74ls00/GameKB/Datasheet/HTK1087B/htk1087b_kb.png

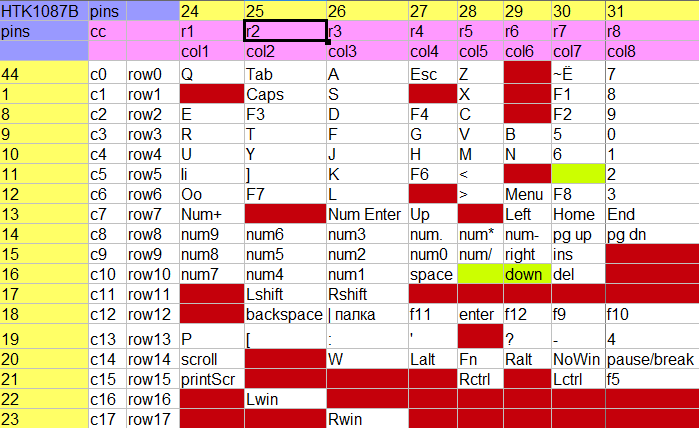
Datasheet/HTK1087B/htk1087b_kb.png
