74ls00/GameKB/Datasheet/HTK1087B/temp1.png

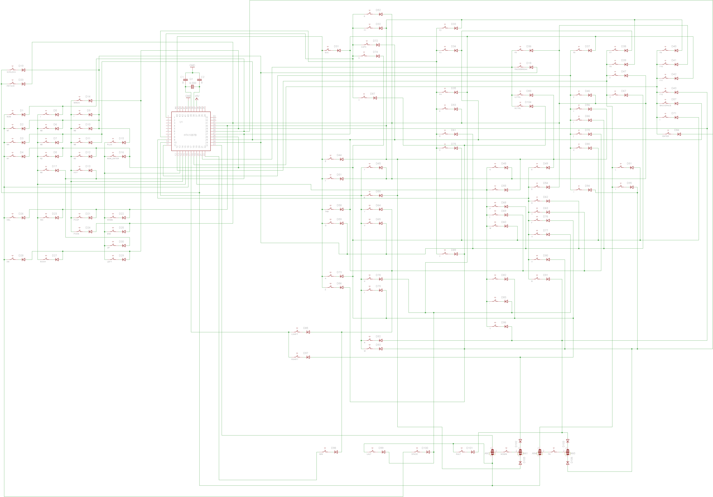
Datasheet/HTK1087B/temp1.png
