74ls00/GameKB/Datasheet/HTK1087B/temp2.png

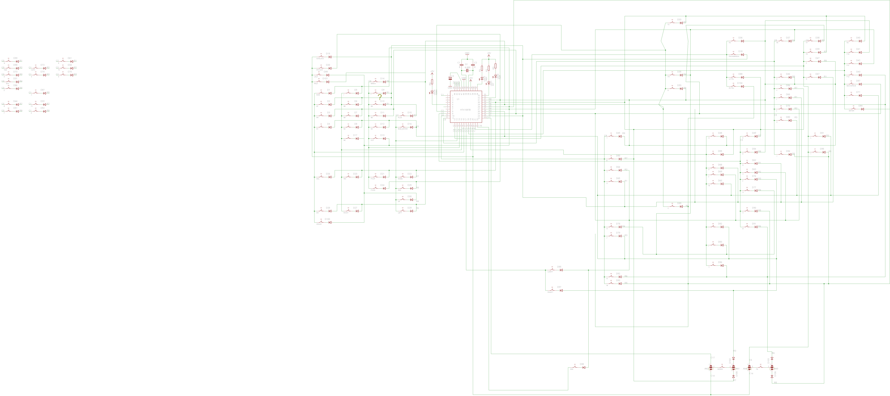
Datasheet/HTK1087B/temp2.png
