74ls00/GameKB/Model/Controller.bmp

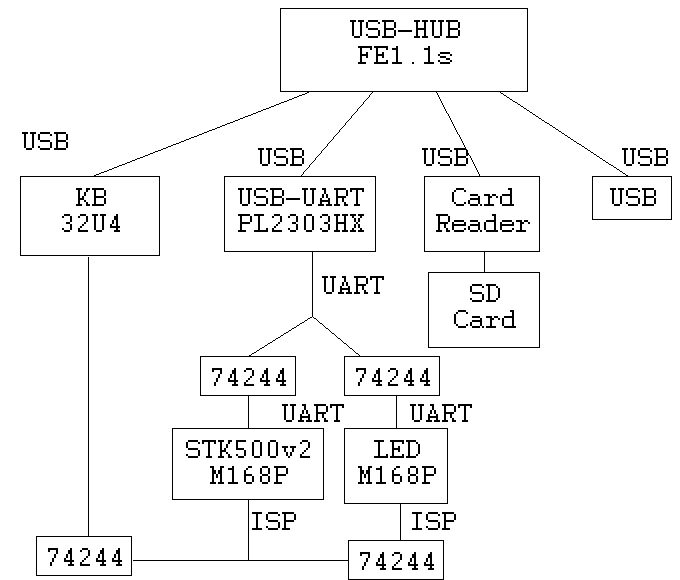
Model/Controller.bmp
