74ls00/GameKB/Model/html/2/Безымянный.png

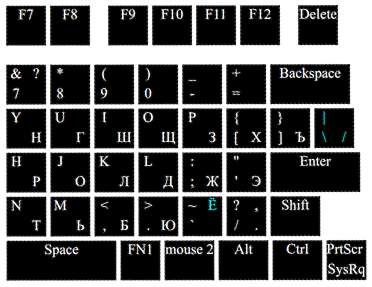
Model/html/2/Безымянный.png
