74ls00/GameKB/Model/html/pic/2.png

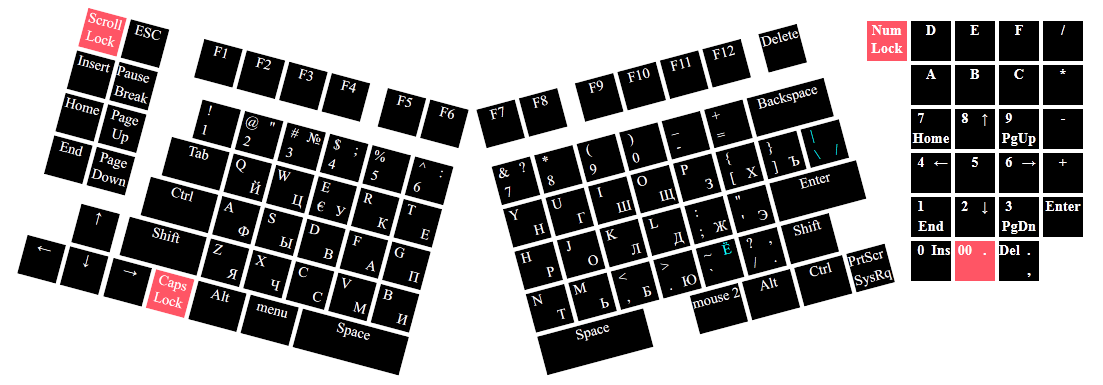
Model/html/pic/2.png
