74ls00/GameKB/Model/key-size/key-size.png

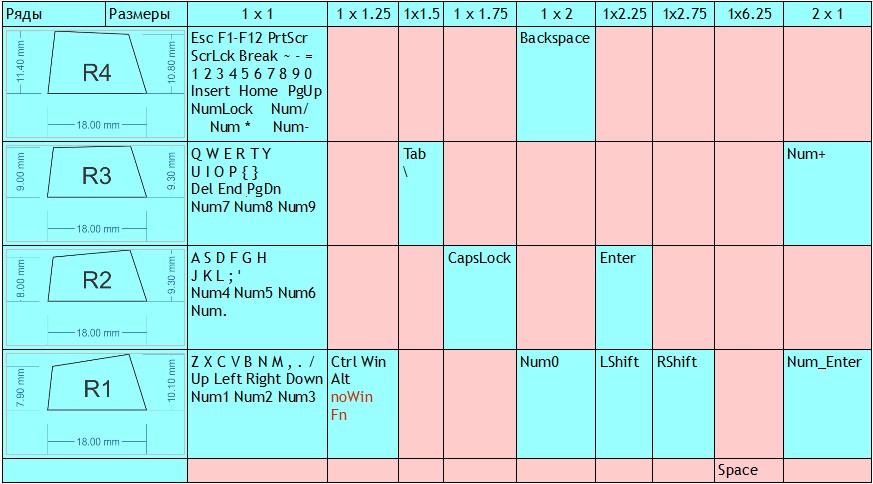
Model/key-size/key-size.png
