74ls00/GameKB/PCB/Controller/png/1.png

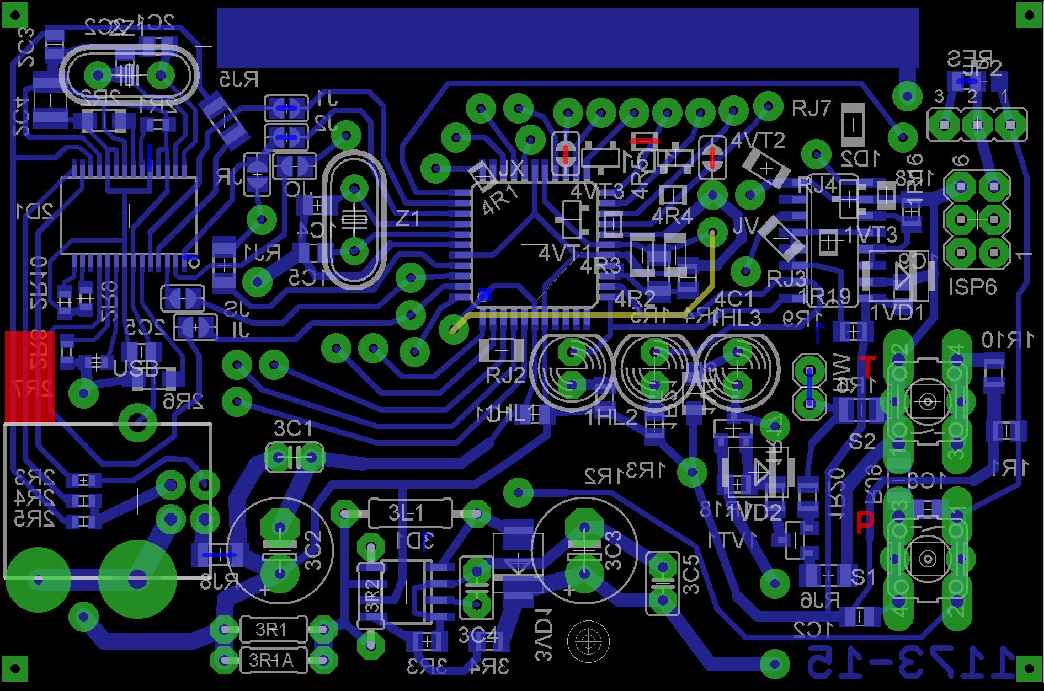
PCB/Controller/png/1.png
