74ls00/GameKB/PCB/Controller/png/1_cr.png

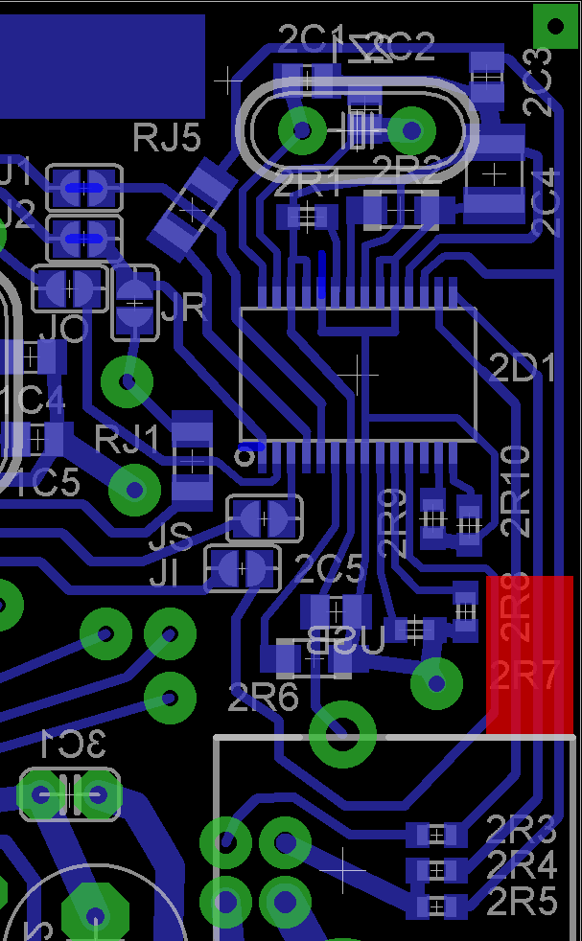
PCB/Controller/png/1_cr.png
