74ls00/GameKB/PCB/Controller/png/101.png

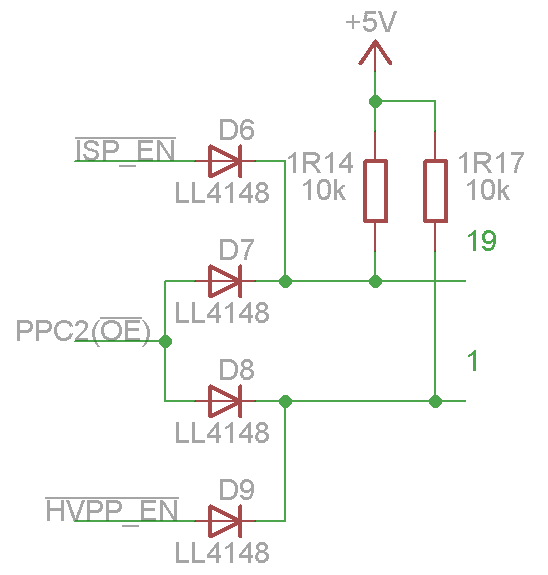
PCB/Controller/png/101.png
