74ls00/GameKB/PCB/Controller/png/102.png

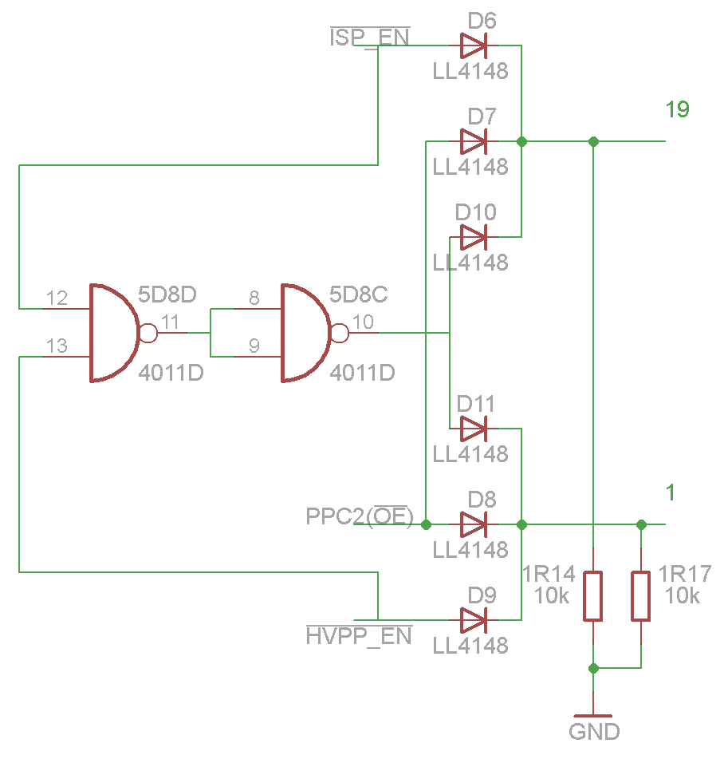
PCB/Controller/png/102.png
