74ls00/GameKB/PCB/Details/enter/HTB1JWZuLXXXXXa.aXXXq6xXFXXX5.jpg

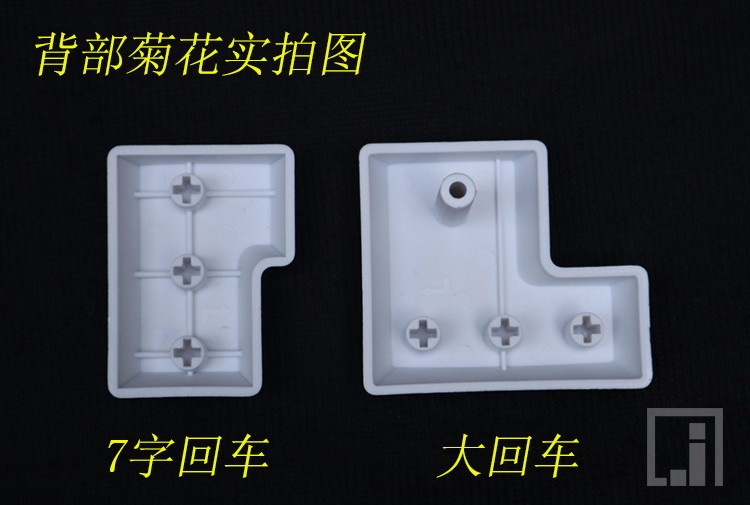
PCB/Details/enter/HTB1JWZuLXXXXXa.aXXXq6xXFXXX5.jpg
