74ls00/GameKB/PCB/Details/enter/HTB1tJs0LXXXXXXZXXXXq6xXFXXXk.jpg

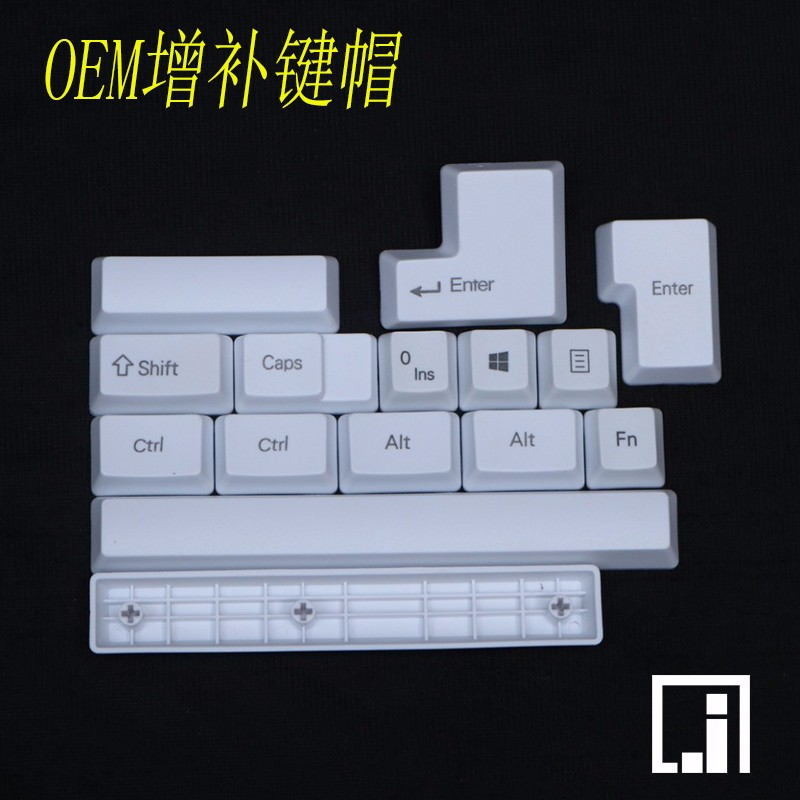
PCB/Details/enter/HTB1tJs0LXXXXXXZXXXXq6xXFXXXk.jpg
