74ls00/GameKB/PCB/Details/stabilizer_frame/stabilizer_frame_i.png

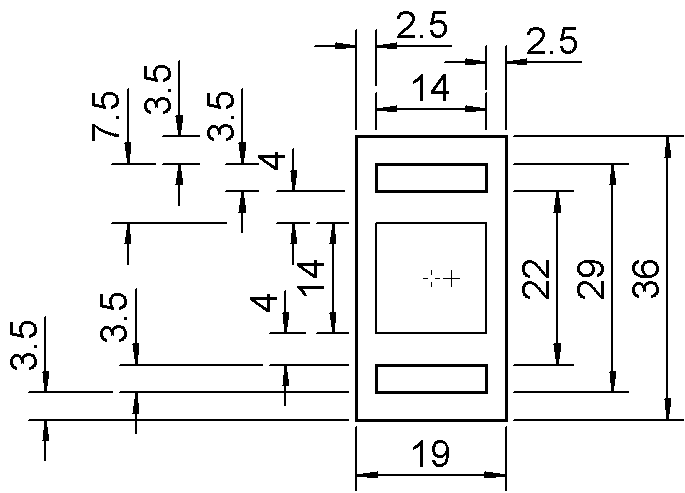
PCB/Details/stabilizer_frame/stabilizer_frame_i.png
