74ls00/GameKB/PCB/keyBoard_A/png/104.png

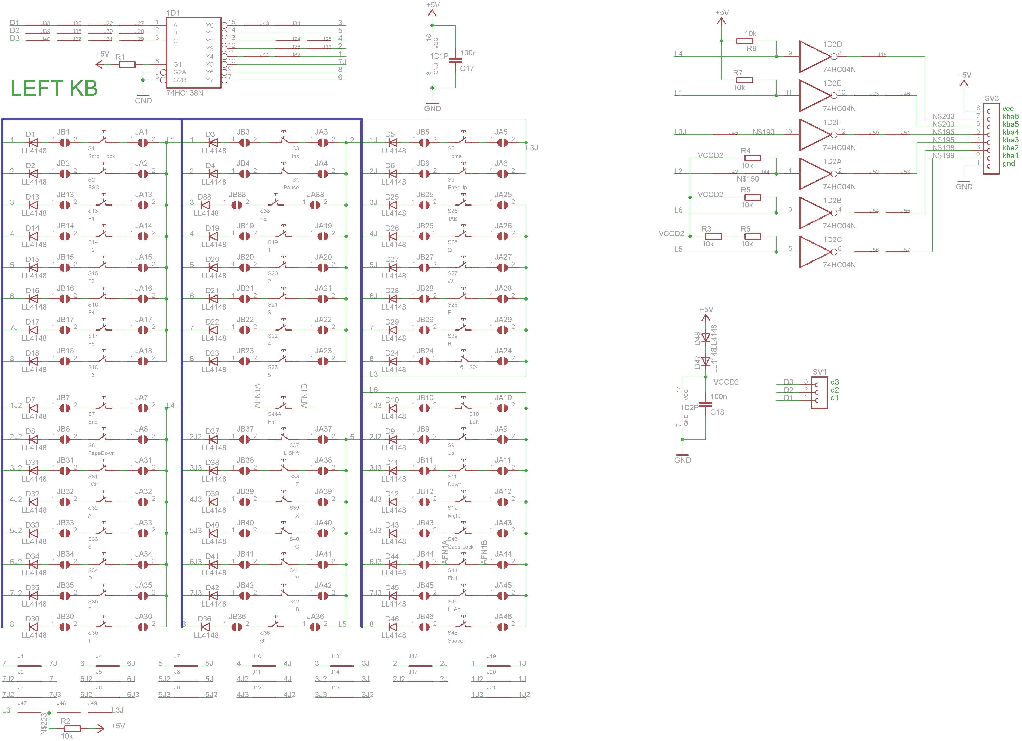
PCB/keyBoard_A/png/104.png
