74ls00/GameKB/PCB/keyBoard_A/png/201.png

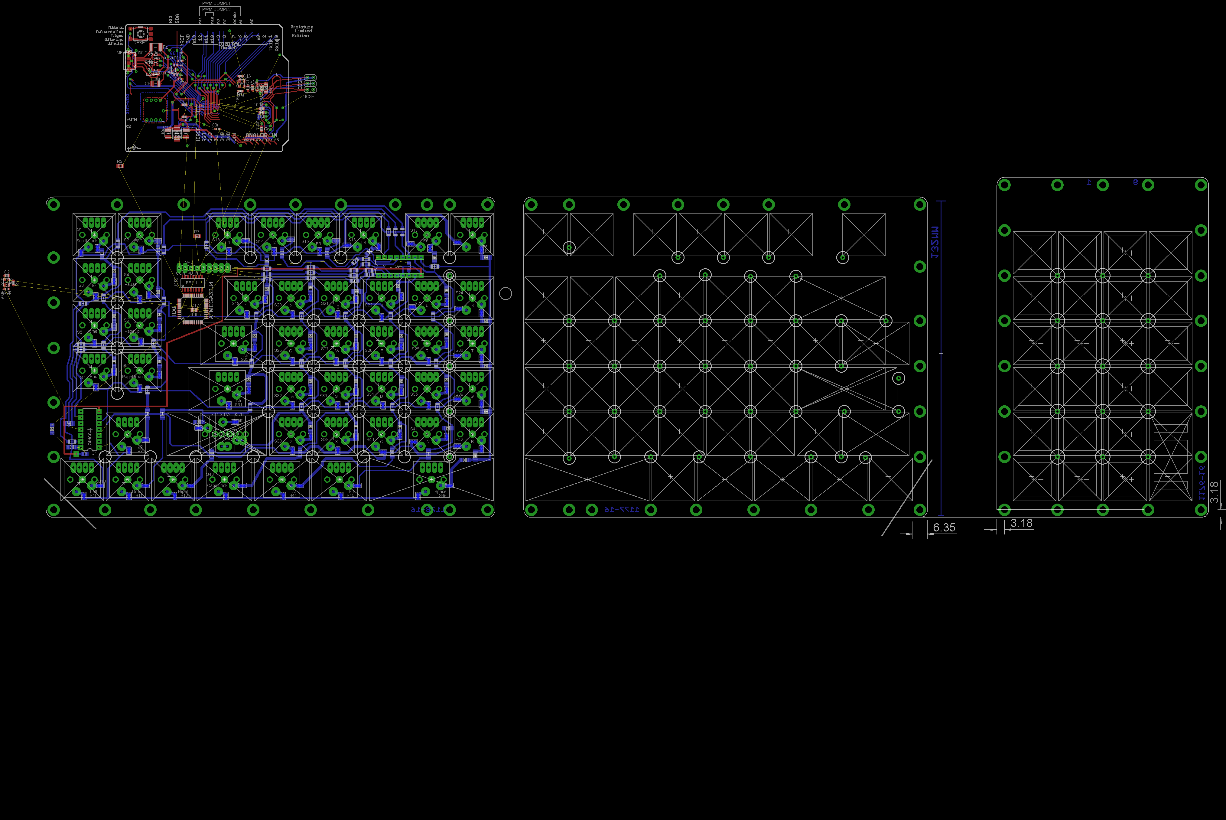
PCB/keyBoard_A/png/201.png
