74ls00/GameKB/PCB/keyBoard_A/png/206.png

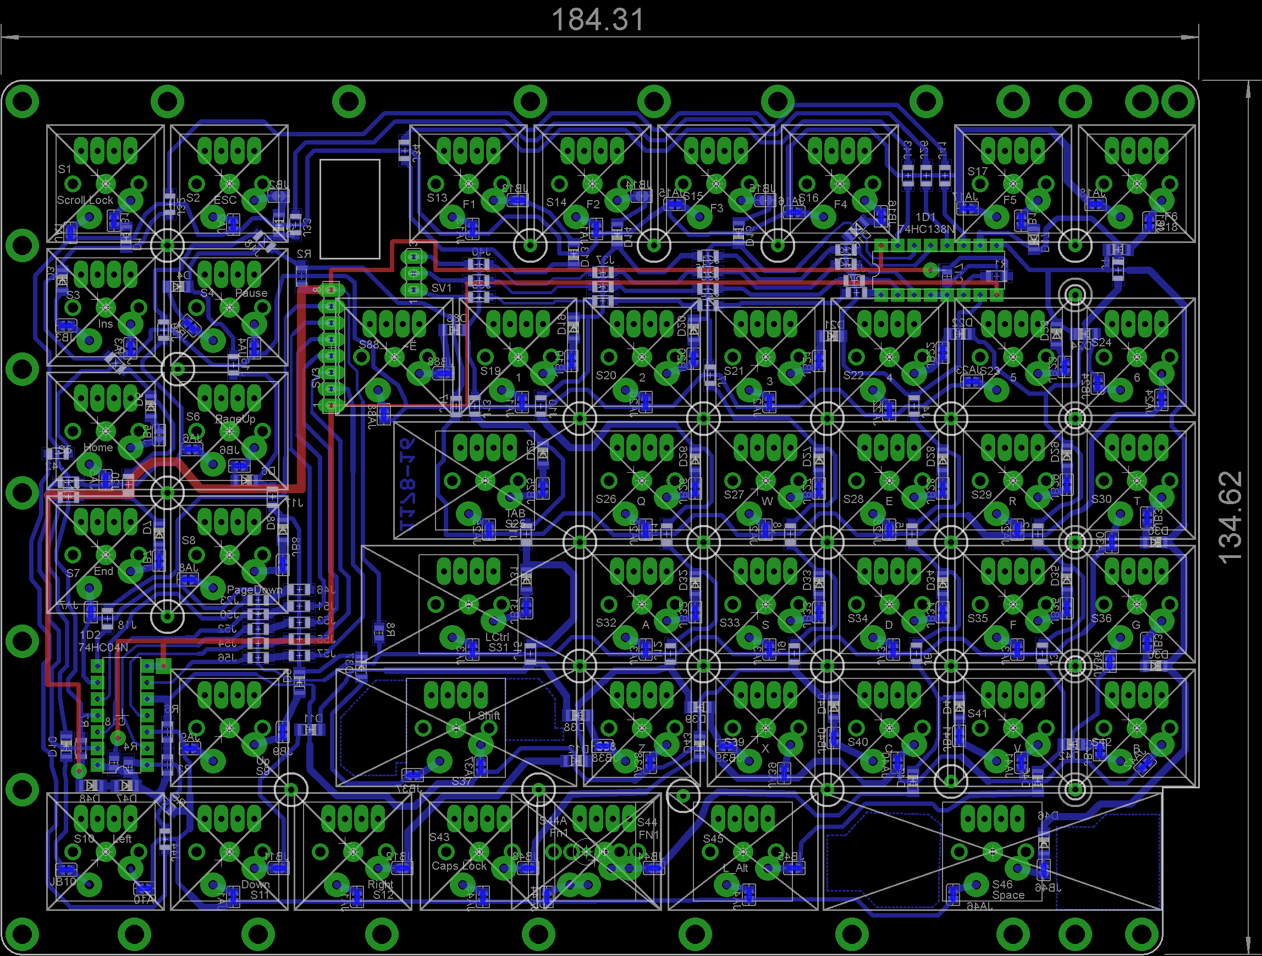
PCB/keyBoard_A/png/206.png
