74ls00/GameKB/PCB/keyBoard_A/png/206_cr.png

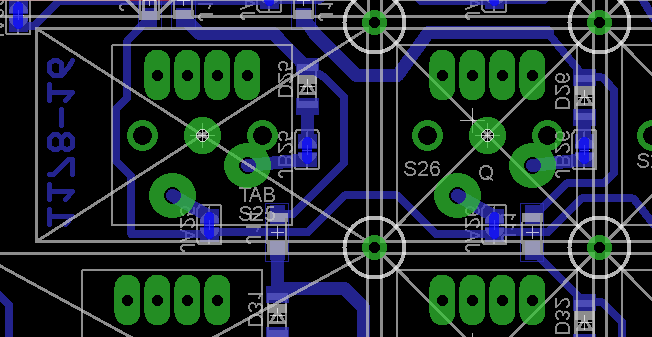
PCB/keyBoard_A/png/206_cr.png
