74ls00/GameKB/PCB/keyBoard_A/png/207.png

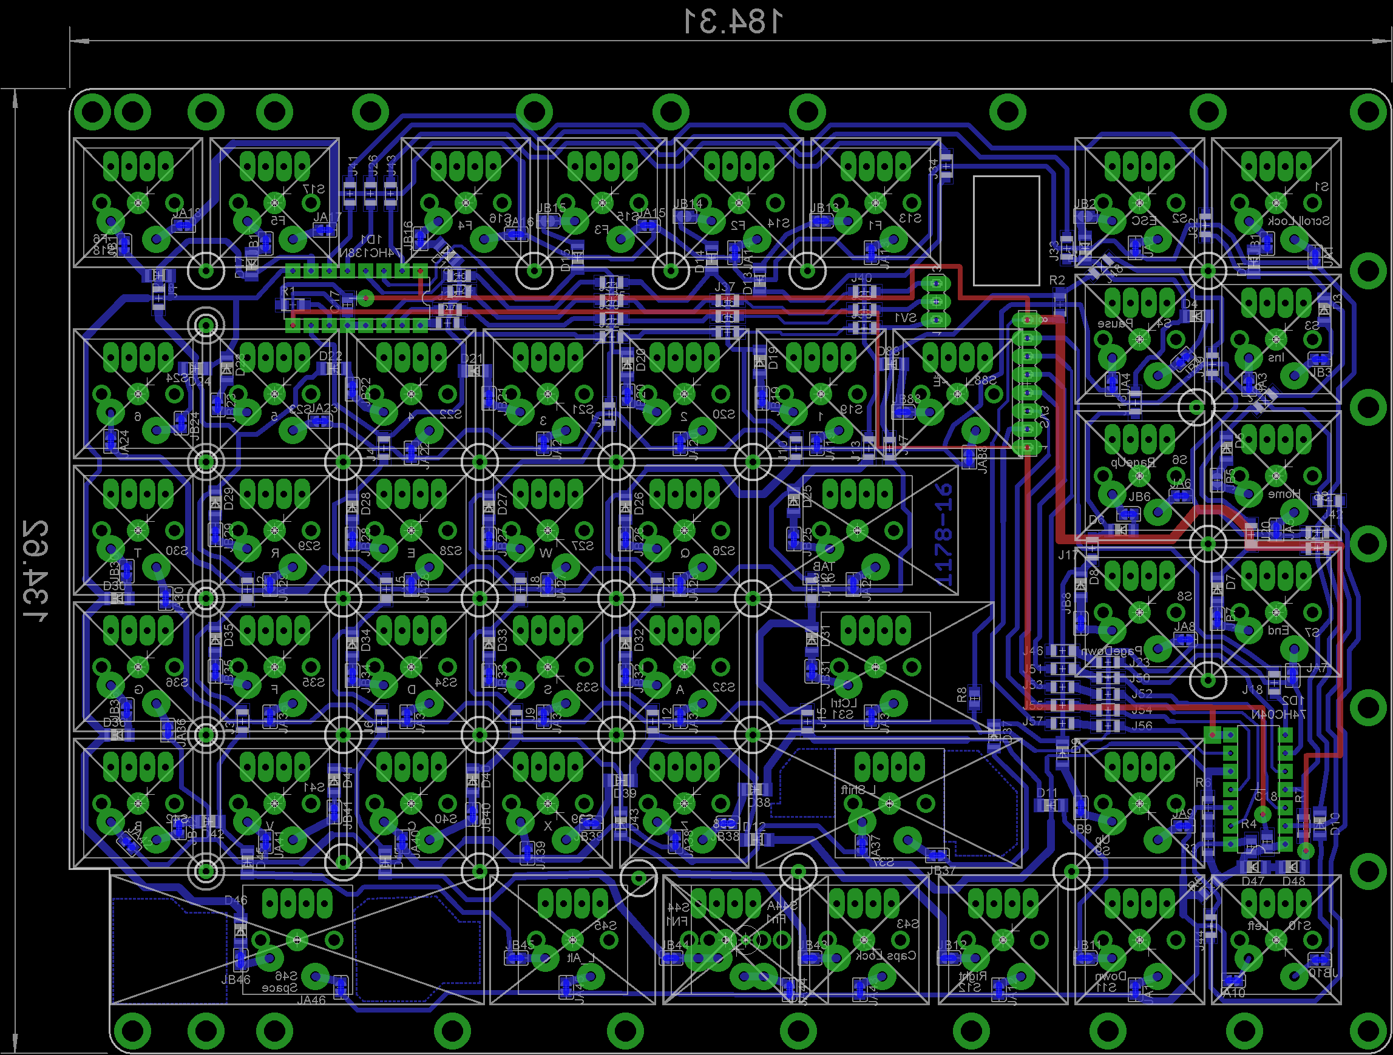
PCB/keyBoard_A/png/207.png
