74ls00/GameKB/PCB/keyBoard_B/png/102.png

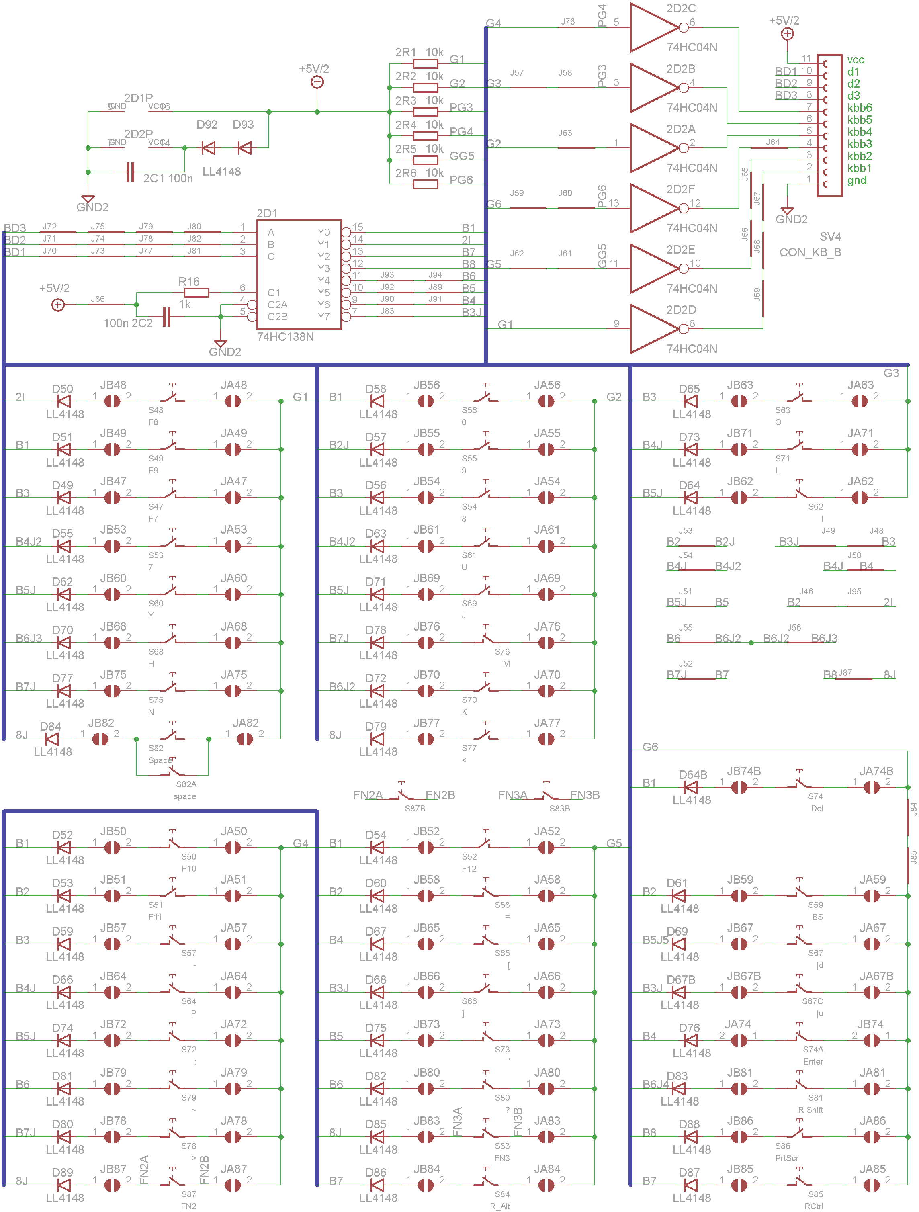
PCB/keyBoard_B/png/102.png
