74ls00/GameKB/PCB/keyBoard_B/png/201.png

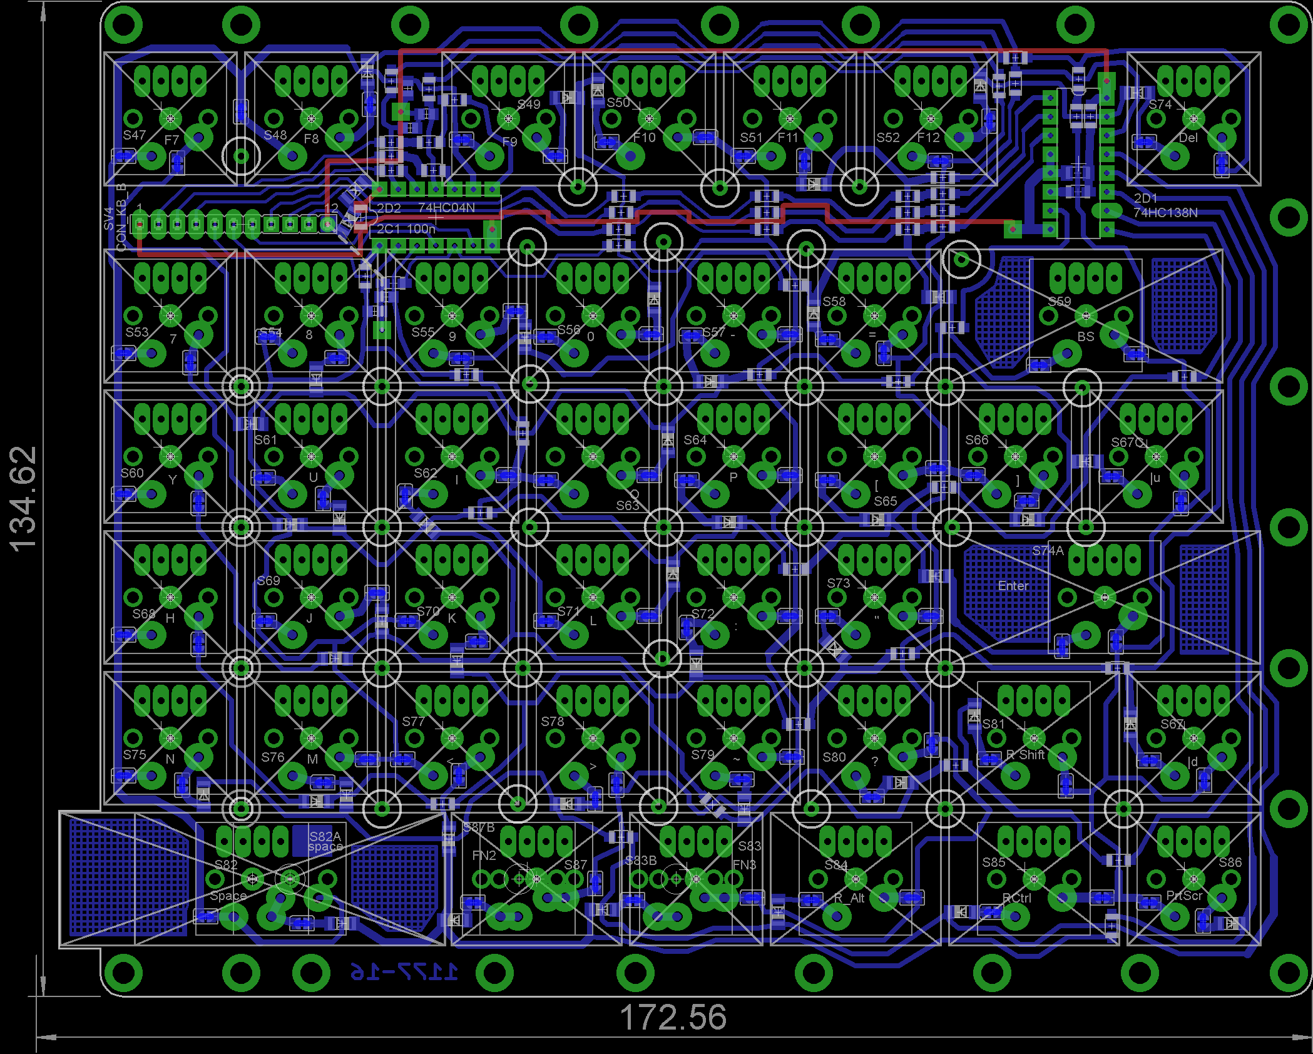
PCB/keyBoard_B/png/201.png
