74ls00/GameKB/PCB/keyBoard_NumPad/png/101.png

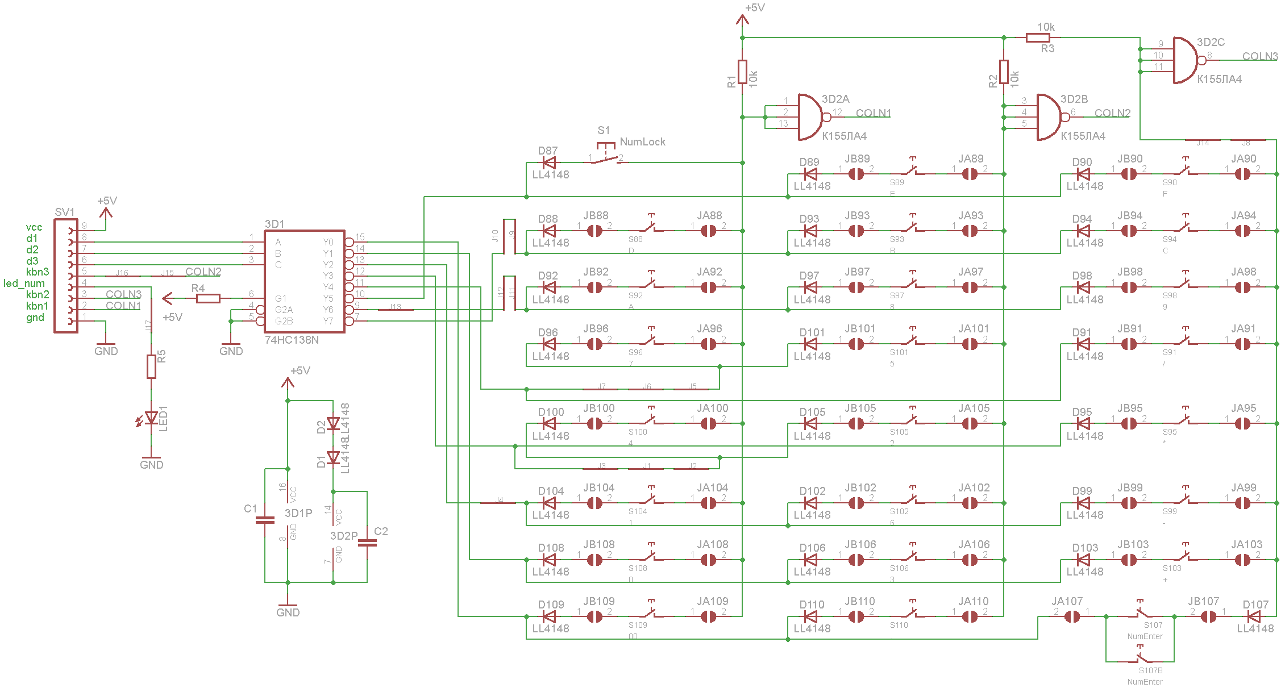
PCB/keyBoard_NumPad/png/101.png
