74ls00/GameKB/PCB/keyBoard_NumPad/png/203.png

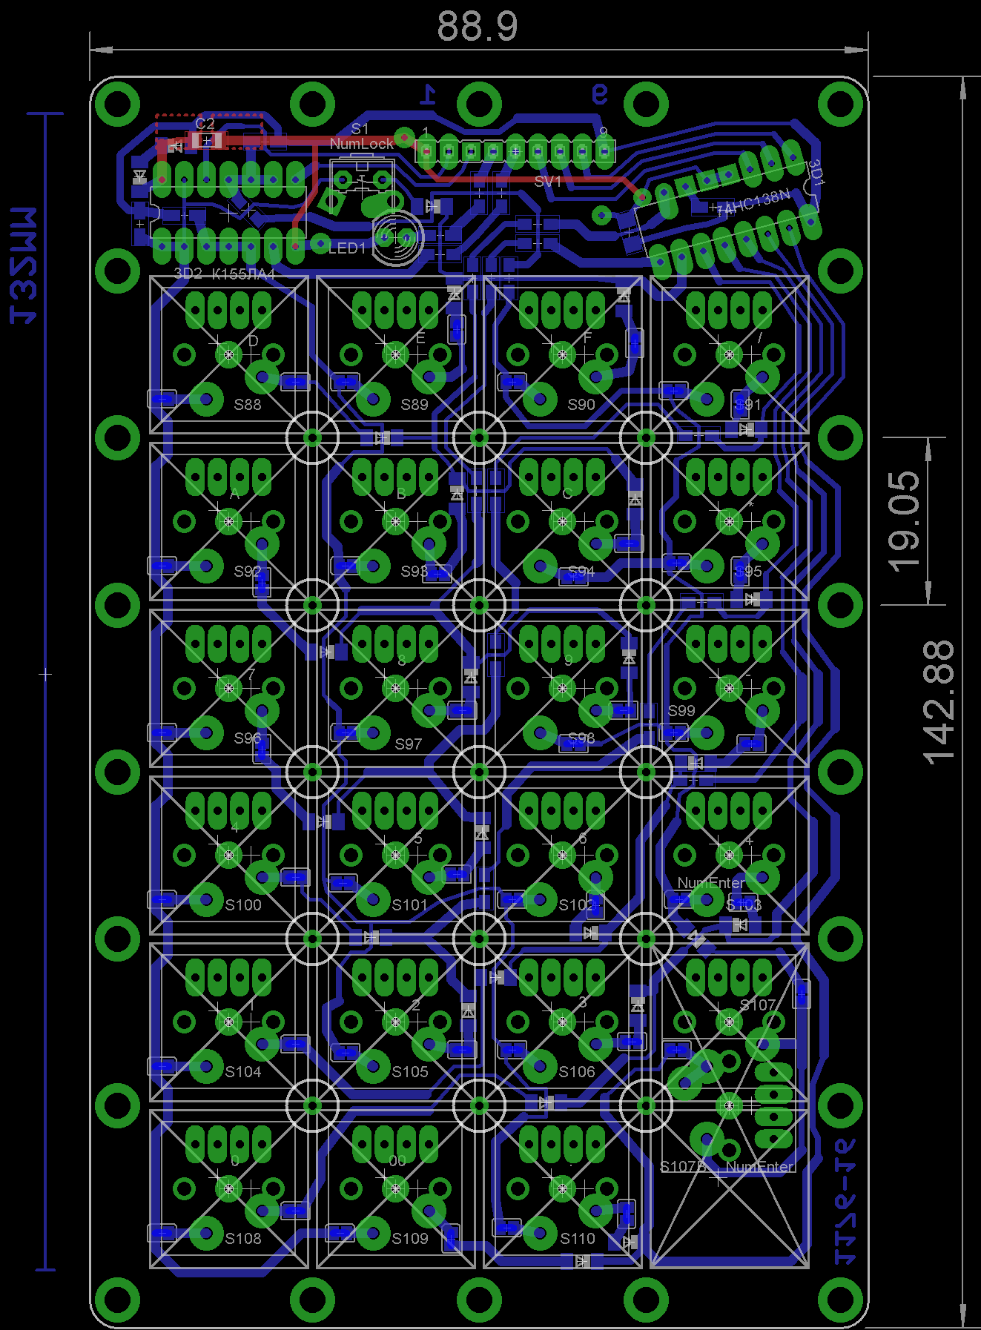
PCB/keyBoard_NumPad/png/203.png
