74ls00/GameKB/PCB/~keyBoard_B/png/103.png

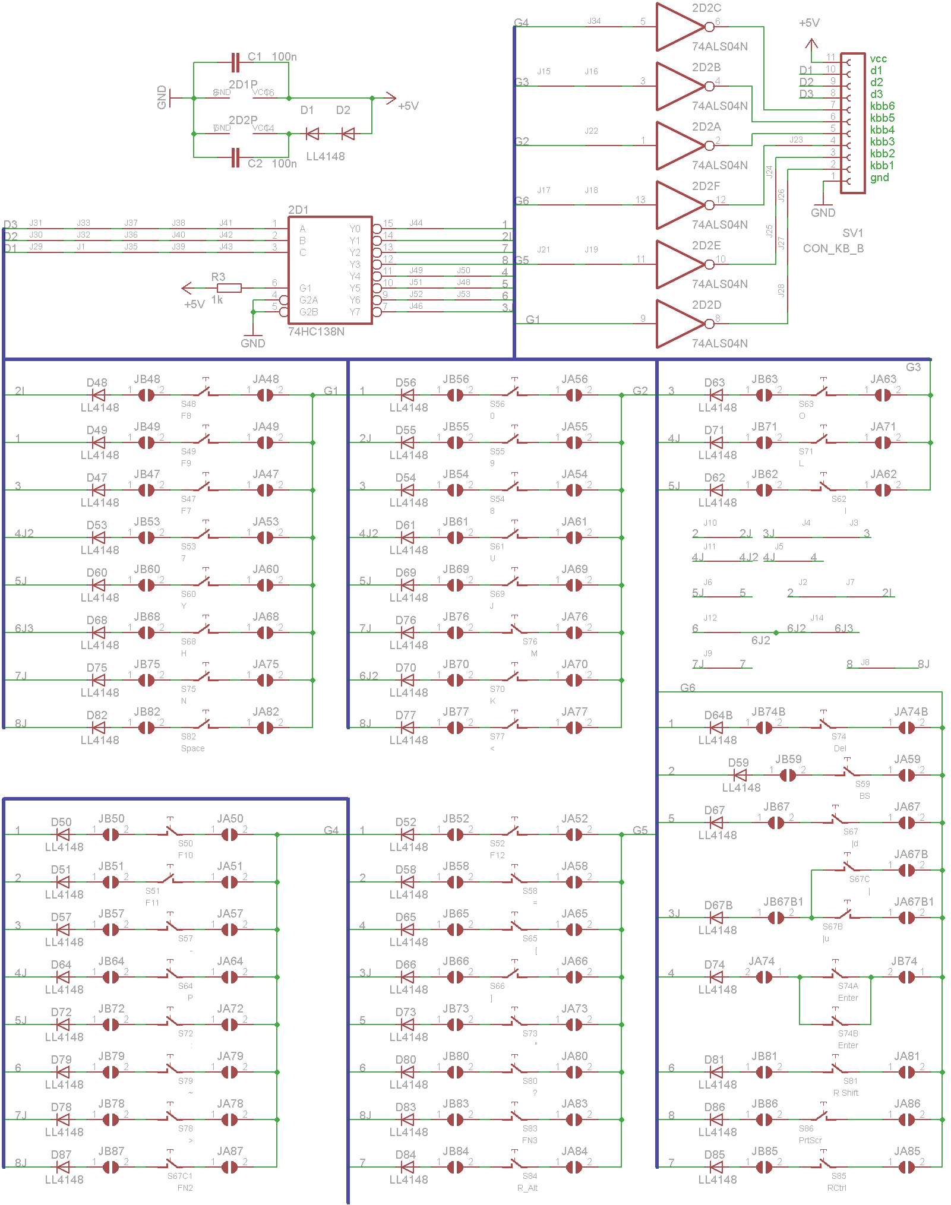
PCB/~keyBoard_B/png/103.png
