74ls00/GameKB/PCB/~keyBoard_B/png/206_cr.png

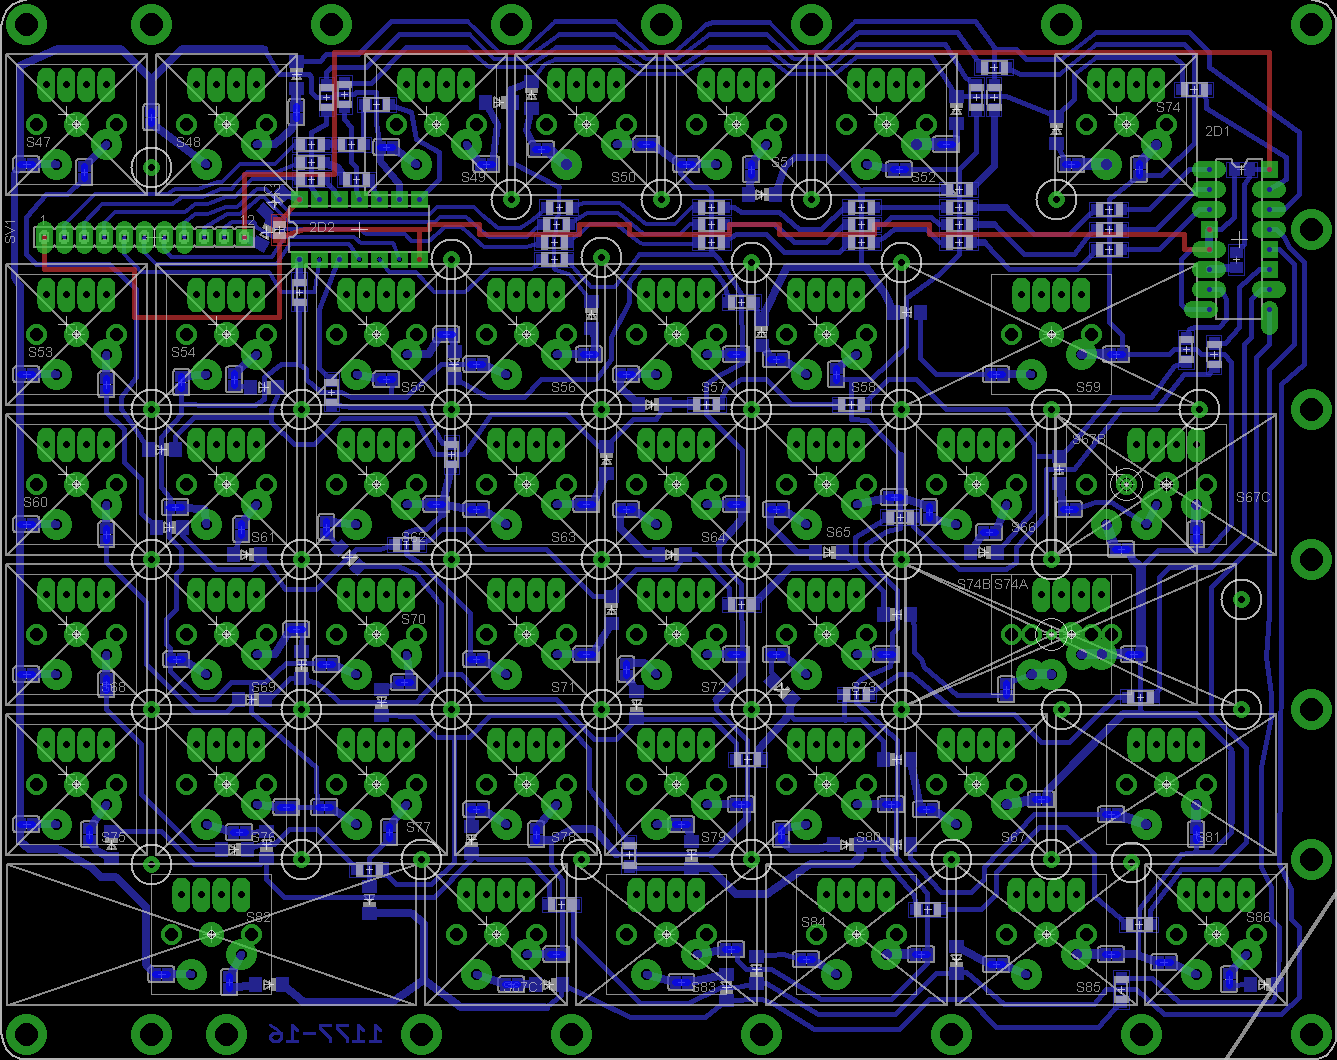
PCB/~keyBoard_B/png/206_cr.png
