74ls00/GameKB/PCB/~keyBoard_B/png/207.png

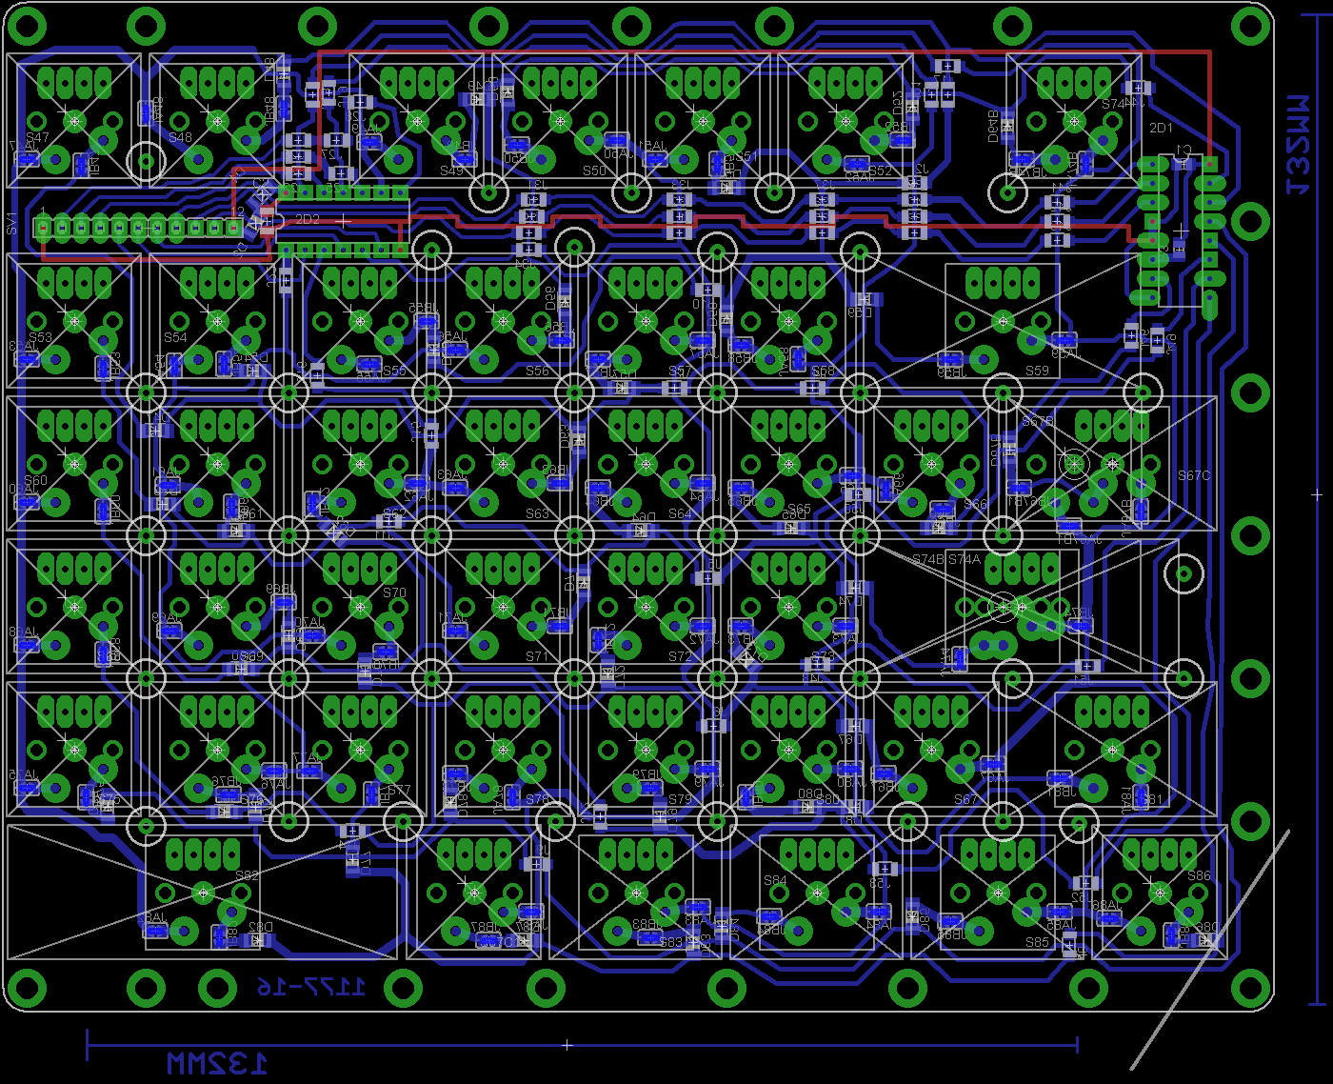
PCB/~keyBoard_B/png/207.png
