74ls00/GameKB/PCB/keyBoard_NumPad/partlist.txt

Partlist

Exported from NumPad.sch at 11.08.2016 8:09:16

EAGLE Version 6.3.0 Copyright (c) 1988-2012 CadSoft

Assembly variant: 

Part     Value          Device       Package      Library  Sheet

3D1      74HC138N       74HC138N     DIL16        detali   1
3D2      Ê155ÈÄ4        74HC10N      DIL14        detali   1
C1                      C-EUC1206    C1206        rcl      1
C2                      C-EUC1206    C1206        rcl      1
D1       LL4148         LL4148       SOD80C       detali   1
D2       LL4148         LL4148       SOD80C       detali   1
D87      LL4148         LL4148       SOD80C       detali   1
D88      LL4148         LL4148       SOD80C       detali   1
D89      LL4148         LL4148       SOD80C       detali   1
D90      LL4148         LL4148       SOD80C       detali   1
D91      LL4148         LL4148       SOD80C       detali   1
D92      LL4148         LL4148       SOD80C       detali   1
D93      LL4148         LL4148       SOD80C       detali   1
D94      LL4148         LL4148       SOD80C       detali   1
D95      LL4148         LL4148       SOD80C       detali   1
D96      LL4148         LL4148       SOD80C       detali   1
D97      LL4148         LL4148       SOD80C       detali   1
D98      LL4148         LL4148       SOD80C       detali   1
D99      LL4148         LL4148       SOD80C       detali   1
D100     LL4148         LL4148       SOD80C       detali   1
D101     LL4148         LL4148       SOD80C       detali   1
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
JB108                   SJ           SJ           detali   1
JB109                   SJ           SJ           detali   1
JB110                   SJ           SJ           detali   1
LED1                    LED5MM       LED5MM       detali   1
R1       10k            R-EU_R1206W  R1206W       rcl      1
R2       10k            R-EU_R1206W  R1206W       rcl      1
R3       10k            R-EU_R1206W  R1206W       rcl      1
R4                      R-EU_R1206W  R1206W       rcl      1
R5                      R-EU_R1206W  R1206W       rcl      1
S1       NumLock        31-XX        B3F-31XX     detali   1
S88      D              CHERRY-MX-4P CHERRY-MX-4P cherrymx 1
S89      E              CHERRY-MX-4P CHERRY-MX-4P cherrymx 1
S90      F              CHERRY-MX-4P CHERRY-MX-4P cherrymx 1
S91      /              CHERRY-MX-4P CHERRY-MX-4P cherrymx 1
S92      A              CHERRY-MX-4P CHERRY-MX-4P cherrymx 1
S93      B              CHERRY-MX-4P CHERRY-MX-4P cherrymx 1
S94      C              CHERRY-MX-4P CHERRY-MX-4P cherrymx 1
S95      *              CHERRY-MX-4P CHERRY-MX-4P cherrymx 1
S96      7              CHERRY-MX-4P CHERRY-MX-4P cherrymx 1
S97      8              CHERRY-MX-4P CHERRY-MX-4P cherrymx 1
S98      9              CHERRY-MX-4P CHERRY-MX-4P cherrymx 1
S99      -              CHERRY-MX-4P CHERRY-MX-4P cherrymx 1
S100     4              CHERRY-MX-4P CHERRY-MX-4P cherrymx 1
S101     5              CHERRY-MX-4P CHERRY-MX-4P cherrymx 1
S102     6              CHERRY-MX-4P CHERRY-MX-4P cherrymx 1
S103     +              CHERRY-MX-4P CHERRY-MX-4P cherrymx 1
S104     1              CHERRY-MX-4P CHERRY-MX-4P cherrymx 1
S105     2              CHERRY-MX-4P CHERRY-MX-4P cherrymx 1
S106     3              CHERRY-MX-4P CHERRY-MX-4P cherrymx 1
S107     NumEnter       CHERRY-MX-4P CHERRY-MX-4P cherrymx 1
S107B    NumEnter       CHERRY-MX-4P CHERRY-MX-4P cherrymx 1
S108     0              CHERRY-MX-4P CHERRY-MX-4P cherrymx 1
S109     00             CHERRY-MX-4P CHERRY-MX-4P cherrymx 1
S110     .              CHERRY-MX-4P CHERRY-MX-4P cherrymx 1
SV1                     FE09-1       FE09         detali   1
