74ls00/GameKB/PCB/~keyBoard_B/partlist.txt

Partlist

Exported from keyBoard_B.sch at 14.08.2016 12:26:25

EAGLE Version 6.3.0 Copyright (c) 1988-2012 CadSoft

Assembly variant: 

Part     Value          Device       Package      Library  Sheet

2D1      74HC138N       74AC138N     DIL16        detali2  1
2D2      74ALS04N       74ALS04N     DIL14        detali2  1
C1       100n           C-EUC0805    C0805        rcl      1
C2       100n           C-EUC1206    C1206        rcl      1
D1       LL4148         LL4148       SOD80C       detali   1
D2       LL4148         LL4148       SOD80C       detali   1
D47      LL4148         LL4148       SOD80C       detali   1
D48      LL4148         LL4148       SOD80C       detali   1
D49      LL4148         LL4148       SOD80C       detali   1
D50      LL4148         LL4148       SOD80C       detali   1
D51      LL4148         LL4148       SOD80C       detali   1
D52      LL4148         LL4148       SOD80C       detali   1
D53      LL4148         LL4148       SOD80C       detali   1
D54      LL4148         LL4148       SOD80C       detali   1
D55      LL4148         LL4148       SOD80C       detali   1
D56      LL4148         LL4148       SOD80C       detali   1
D57      LL4148         LL4148       SOD80C       detali   1
D58      LL4148         LL4148       SOD80C       detali   1
D59      LL4148         LL4148       SOD80C       detali   1
D60      LL4148         LL4148       SOD80C       detali   1
D61      LL4148         LL4148       SOD80C       detali   1
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
S49      F9             CHERRY-MX-4P CHERRY-MX-4P cherrymx 1
S50      F10            CHERRY-MX-4P CHERRY-MX-4P cherrymx 1
S51      F11            CHERRY-MX-4P CHERRY-MX-4P cherrymx 1
S52      F12            CHERRY-MX-4P CHERRY-MX-4P cherrymx 1
S53      7              CHERRY-MX-4P CHERRY-MX-4P cherrymx 1
S54      8              CHERRY-MX-4P CHERRY-MX-4P cherrymx 1
S55      9              CHERRY-MX-4P CHERRY-MX-4P cherrymx 1
S56      0              CHERRY-MX-4P CHERRY-MX-4P cherrymx 1
S57      -              CHERRY-MX-4P CHERRY-MX-4P cherrymx 1
S58      =              CHERRY-MX-4P CHERRY-MX-4P cherrymx 1
S59      BS             CHERRY-MX-4P CHERRY-MX-4P cherrymx 1
S60      Y              CHERRY-MX-4P CHERRY-MX-4P cherrymx 1
S61      U              CHERRY-MX-4P CHERRY-MX-4P cherrymx 1
S62      I              CHERRY-MX-4P CHERRY-MX-4P cherrymx 1
S63      O              CHERRY-MX-4P CHERRY-MX-4P cherrymx 1
S64      P              CHERRY-MX-4P CHERRY-MX-4P cherrymx 1
S65      [              CHERRY-MX-4P CHERRY-MX-4P cherrymx 1
S66      ]              CHERRY-MX-4P CHERRY-MX-4P cherrymx 1
S67      |d             CHERRY-MX-4P CHERRY-MX-4P cherrymx 1
S67B     |u             CHERRY-MX    CHERRY-MX    cherrymx 1
S67C     |              CHERRY-MX-4P CHERRY-MX-4P cherrymx 1
S67C1    FN2            CHERRY-MX-4P CHERRY-MX-4P cherrymx 1
S68      H              CHERRY-MX-4P CHERRY-MX-4P cherrymx 1
S69      J              CHERRY-MX-4P CHERRY-MX-4P cherrymx 1
S70      K              CHERRY-MX-4P CHERRY-MX-4P cherrymx 1
S71      L              CHERRY-MX-4P CHERRY-MX-4P cherrymx 1
S72      :              CHERRY-MX-4P CHERRY-MX-4P cherrymx 1
S73      "              CHERRY-MX-4P CHERRY-MX-4P cherrymx 1
S74      Del            CHERRY-MX-4P CHERRY-MX-4P cherrymx 1
S74A     Enter          CHERRY-MX-4P CHERRY-MX-4P cherrymx 1
S74B     Enter          CHERRY-MX    CHERRY-MX    cherrymx 1
S75      N              CHERRY-MX-4P CHERRY-MX-4P cherrymx 1
S76      M              CHERRY-MX-4P CHERRY-MX-4P cherrymx 1
S77      <              CHERRY-MX-4P CHERRY-MX-4P cherrymx 1
S78      >              CHERRY-MX-4P CHERRY-MX-4P cherrymx 1
S79      ~              CHERRY-MX-4P CHERRY-MX-4P cherrymx 1
S80      ?              CHERRY-MX-4P CHERRY-MX-4P cherrymx 1
S81      R Shift        CHERRY-MX-4P CHERRY-MX-4P cherrymx 1
S82      Space          CHERRY-MX-4P CHERRY-MX-4P cherrymx 1
S83      FN3            CHERRY-MX-4P CHERRY-MX-4P cherrymx 1
S84      R_Alt          CHERRY-MX-4P CHERRY-MX-4P cherrymx 1
S85      RCtrl          CHERRY-MX-4P CHERRY-MX-4P cherrymx 1
S86      PrtScr         CHERRY-MX-4P CHERRY-MX-4P cherrymx 1
SV1      CON_KB_B       FE12-1       FE12         detali2  1
